hatobus/SCCP_auto_drive/dataset/sample/signal_beep.jpg

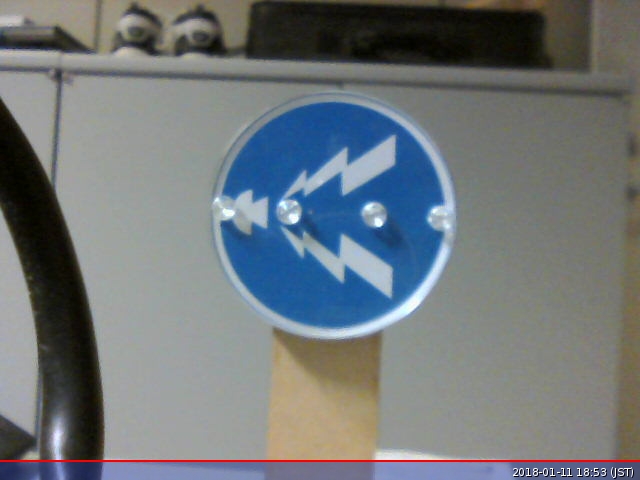
dataset/sample/signal_beep.jpg
