hatobus/SCCP_auto_drive/dataset/sample/signal_stop.jpg

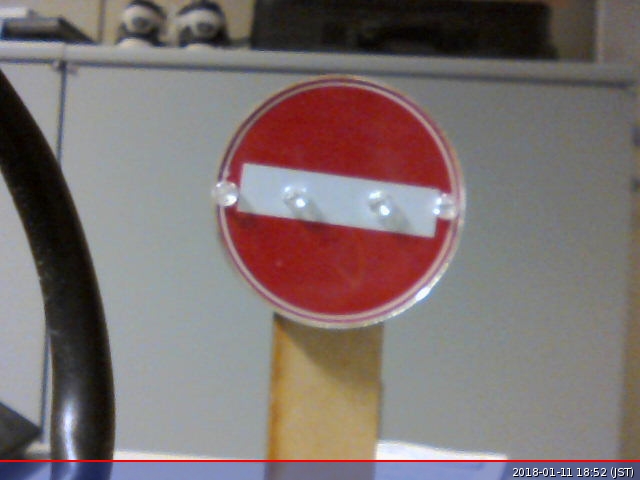
dataset/sample/signal_stop.jpg
