hatobus/SCCP_auto_drive/program/LCD_display/LCD.py

#coding:utf-8
import smbus
import time

# from Adafruit_CharLCD import Adafruit_CharLCD

# Define some device parameters
I2C_ADDR  = 0x27 # I2C device address, if any error, change this address to 0x3f
LCD_WIDTH = 16   # Maximum characters per line

# Define some device constants
LCD_CHR = 1 # Mode - Sending data
LCD_CMD = 0 # Mode - Sending command

LCD_LINE_1 = 0x80 # LCD RAM address for the 1st line
LCD_LINE_2 = 0xC0 # LCD RAM address for the 2nd line
LCD_LINE_3 = 0x94 # LCD RAM address for the 3rd line
LCD_LINE_4 = 0xD4 # LCD RAM address for the 4th line

LCD_BACKLIGHT  = 0x08  # On
#LCD_BACKLIGHT = 0x00  # Off

ENABLE = 0b00000100 # Enable bit

# Timing constants
E_PULSE = 0.0005
E_DELAY = 0.0005

#Open I2C interface
bus = smbus.SMBus(1) # Rev 2 Pi uses 1

class LCD():
    
    def __init__(self):
        pass

    def lcd_init(self):
      # Initialise display
        self.lcd_byte(0x33,LCD_CMD) # 110011 Initialise
        self.lcd_byte(0x32,LCD_CMD) # 110010 Initialise
        self.lcd_byte(0x06,LCD_CMD) # 000110 Cursor move direction
        self.lcd_byte(0x0C,LCD_CMD) # 001100 Display On,Cursor Off, Blink Off 
        self.lcd_byte(0x28,LCD_CMD) # 101000 Data length, number of lines, font size
        self.lcd_byte(0x01,LCD_CMD) # 000001 Clear display
        time.sleep(E_DELAY)

    def lcd_byte(self,bits, mode):
      # Send byte to data pins
      # bits = the data
      # mode = 1 for data
      #        0 for command

        bits_high = mode | (bits & 0xF0) | LCD_BACKLIGHT
        bits_low = mode | ((bits<<4) & 0xF0) | LCD_BACKLIGHT

      # High bits
        bus.write_byte(I2C_ADDR, bits_high)
        self.lcd_toggle_enable(bits_high)

      # Low bits
        bus.write_byte(I2C_ADDR, bits_low)
        self.lcd_toggle_enable(bits_low)

    def lcd_toggle_enable(self,bits):
      # Toggle enable
        time.sleep(E_DELAY)
        bus.write_byte(I2C_ADDR, (bits | ENABLE))
        time.sleep(E_PULSE)
        bus.write_byte(I2C_ADDR,(bits & ~ENABLE))
        time.sleep(E_DELAY)

    def lcd_string(self,message,line):
      # Send string to display

        message = message.ljust(LCD_WIDTH," ")

        self.lcd_byte(line, LCD_CMD)

        for i in range(LCD_WIDTH):
            self.lcd_byte(ord(message[i]),LCD_CHR)
            
            
    def LCD_LINE1(self,messege_upper,times):
        messege_upper = str(messege_upper)
        self.lcd_string(messege_upper,LCD_LINE_1)
        time.sleep(times)
        self.lcd_byte(0x01, LCD_CMD)
        
    def LCD_LINE2(self,messege_lower,times):
        messege_lower = str(messege_lower)
        self.lcd_string(messege_lower,LCD_LINE_2)
        time.sleep(times)
        self.lcd_byte(0x01, LCD_CMD)
        
    def LCD_Full(self,messege_upper,messege_lower,times):
        messege_upper = str(messege_upper)
        messege_lower = str(messege_lower)
        self.lcd_string(messege_upper,LCD_LINE_1)
        self.lcd_string(messege_lower,LCD_LINE_2)
        time.sleep(times)
        self.lcd_byte(0x01, LCD_CMD)
        
